cmitchell716/Design1Proj2/sketches/input_combined/input_combined.ino

#include "MPU9250.h"
#include <Wire.h>
#include <SoftwareSerial.h>
#include <TinyGPS.h>

TinyGPS gps;
SoftwareSerial ss(4, 5);
MPU9250 mpu;
bool newGPS = false;
bool newIMU = false;
float accX, accY, accZ, magX, magY, magZ, gyrX, gyrY, gyrZ;

void setup() {
  Serial.begin(115200);
  ss.begin(9600);
  Wire.begin();
  delay(2000);

  if (!mpu.setup(0x68)) {  
      while (1) {
          Serial.println(F("MPU connection failed."));
          delay(5000);
      }
  }
  else {
    mpu.setAccBias(36.19, 3.86, 54.43);
    mpu.setGyroBias(-1.20, 1.95, -0.08);
    mpu.setMagBias(128.27, -144.56, -176.65);
    mpu.setMagScale(1.18, 1.03, 0.85);
    mpu.setMagneticDeclination(3.08);
  }

}

void loop() {
  if (mpu.available()) {
        mpu.update_accel_gyro();
        mpu.update_mag();
        //static uint32_t prev_ms = millis();
        //if (millis() > prev_ms + 100) {
            //save_IMU_measurements();
            //newIMU = true;
            //prev_ms = millis();
        //}
        save_IMU_measurements();
        newIMU = true;
  }

  for (unsigned long start = millis(); millis() - start < 5;)
  {
    while (ss.available())
    {
      char c = ss.read();
      if (gps.encode(c))  
        newGPS = true;
    }
  }
  
  if(newIMU && newGPS) {
    print_IMU_measurements();
    newIMU = false;
    print_GPS_measurements();
    newGPS = false;
  }

}

void save_IMU_measurements(){
  accX = mpu.getAccX();
  accY = mpu.getAccY();
  accZ = mpu.getAccZ();
  magX = mpu.getMagX();
  magY = mpu.getMagY(); 
  magZ = mpu.getMagZ(); 
  gyrX = mpu.getGyroX();
  gyrY = mpu.getGyroY();
  gyrZ = mpu.getGyroZ();
}

void print_IMU_measurements() {
    Serial.print("Acceleration X, Y, Z: ");
    Serial.print(accX, 2);
    Serial.print(", ");
    Serial.print(accY, 2);
    Serial.print(", ");
    Serial.print(accZ, 2);
    Serial.print("  ");
    Serial.print("Mag X, Y, Z: ");
    Serial.print(magX, 2);
    Serial.print(", ");
    Serial.print(magY, 2);
    Serial.print(", ");
    Serial.print(magZ, 2);
    Serial.print(", ");
    Serial.print("Gyro X, Y, Z: ");
    Serial.print(mpu.getGyroX(), 2);
    Serial.print(", ");
    Serial.print(mpu.getGyroY(), 2);
    Serial.print(", ");
    Serial.println(mpu.getGyroZ(), 2);
}

void print_GPS_measurements() {
  float flat, flon;
  unsigned long age, alt;
  gps.f_get_position(&flat, &flon, &age);
  Serial.print("LAT=");
  Serial.print(flat == TinyGPS::GPS_INVALID_F_ANGLE ? 0.0 : flat, 6);
  Serial.print(" LON=");
  Serial.print(flon == TinyGPS::GPS_INVALID_F_ANGLE ? 0.0 : flon, 6);
  Serial.print(" ALT=");
  Serial.print(alt == TinyGPS::GPS_INVALID_ALTITUDE ? 0 : gps.altitude());
  Serial.print(" SAT=");
  Serial.println(gps.satellites() == TinyGPS::GPS_INVALID_SATELLITES ? 0 : gps.satellites());
}
